nikoschalikias/pcb-n-dap/ord/SKMBT_C28015102014001.pdf

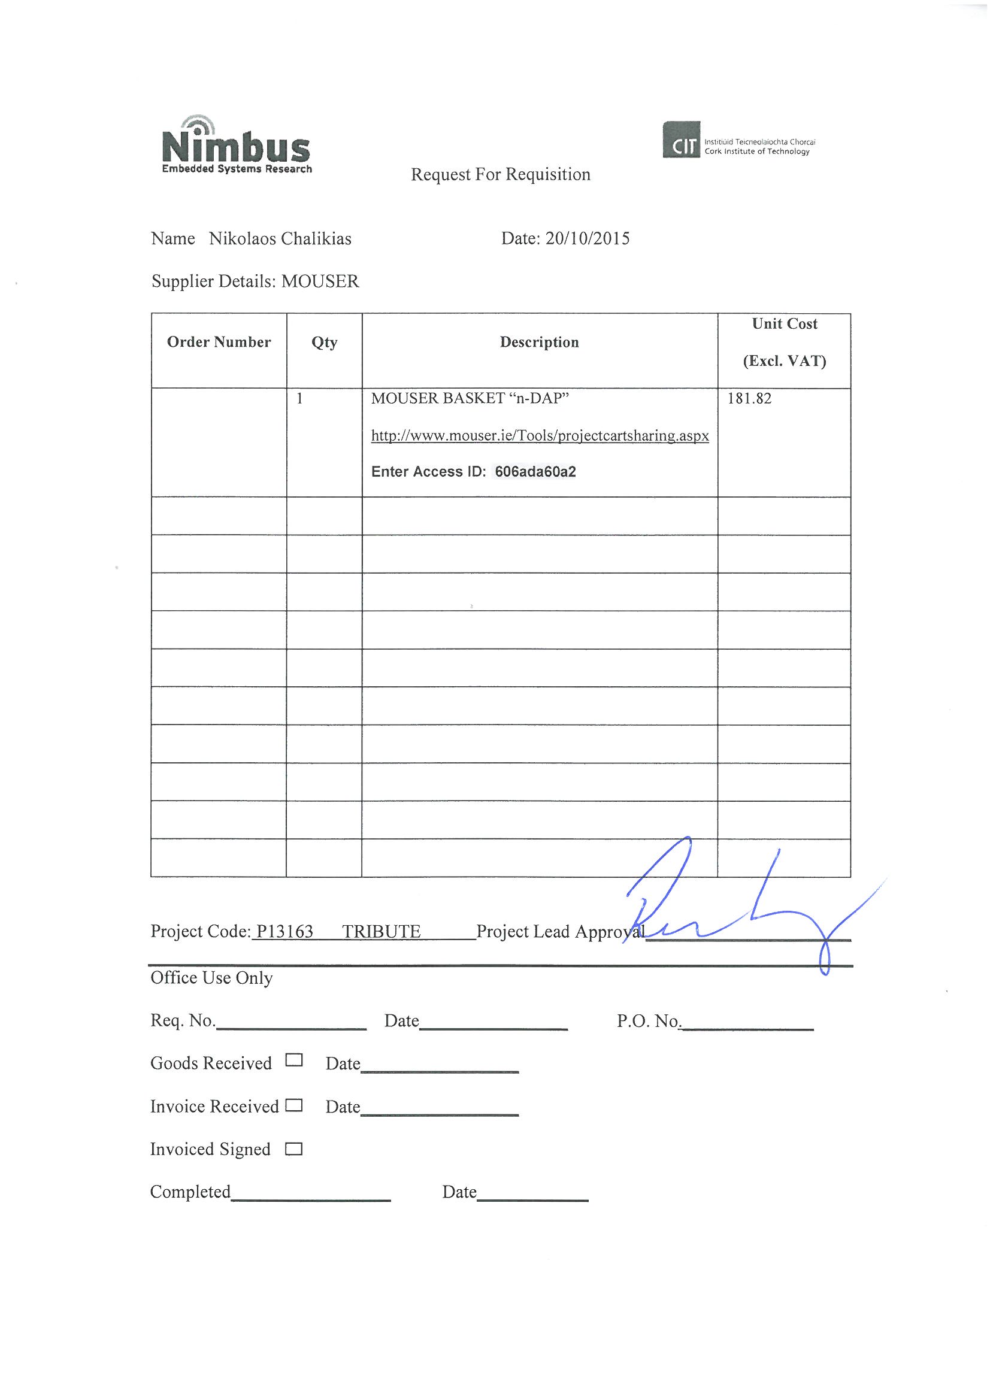
[picture p5: page 1]
