nikoschalikias/pcb-n-dap/ord/SKMBT_C28015101914000.pdf

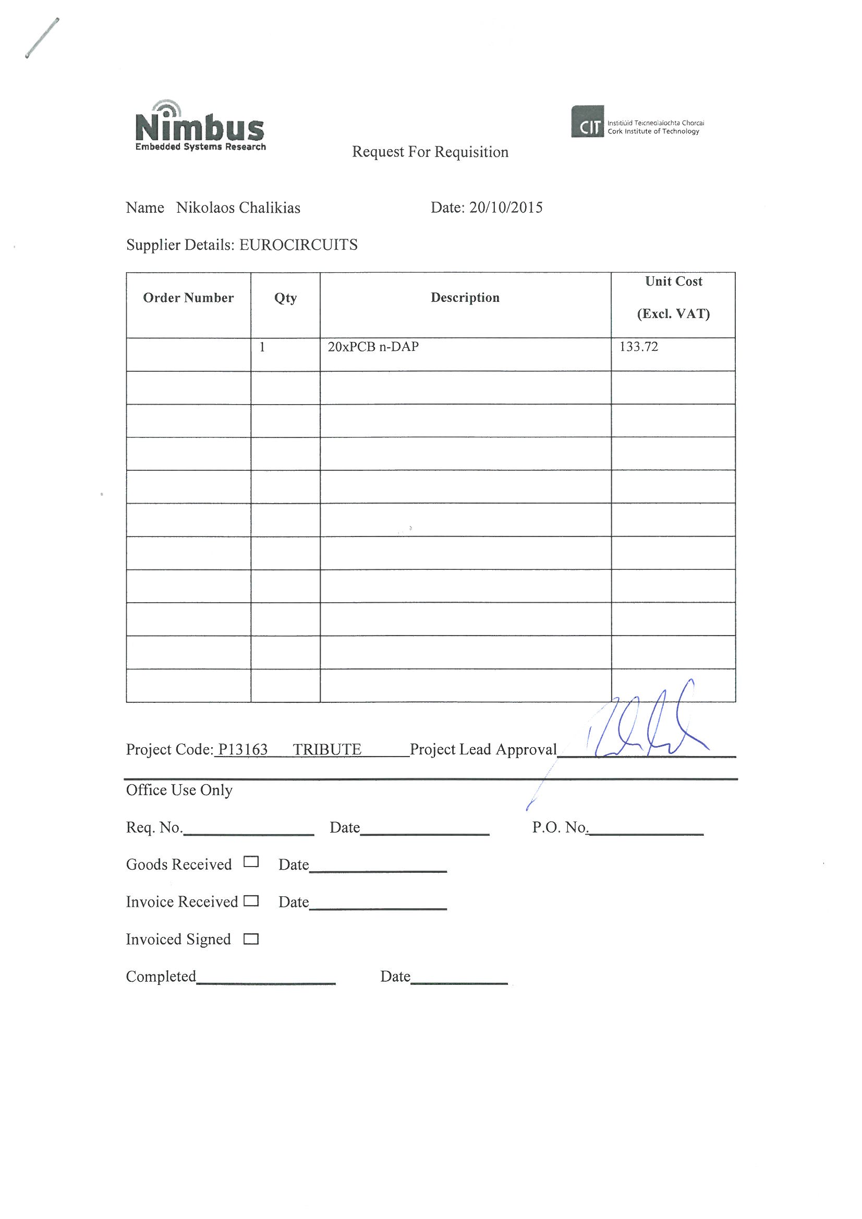
[picture p6: page 1]
