nikoschalikias/pcb-n-dap/template/3D.PDF

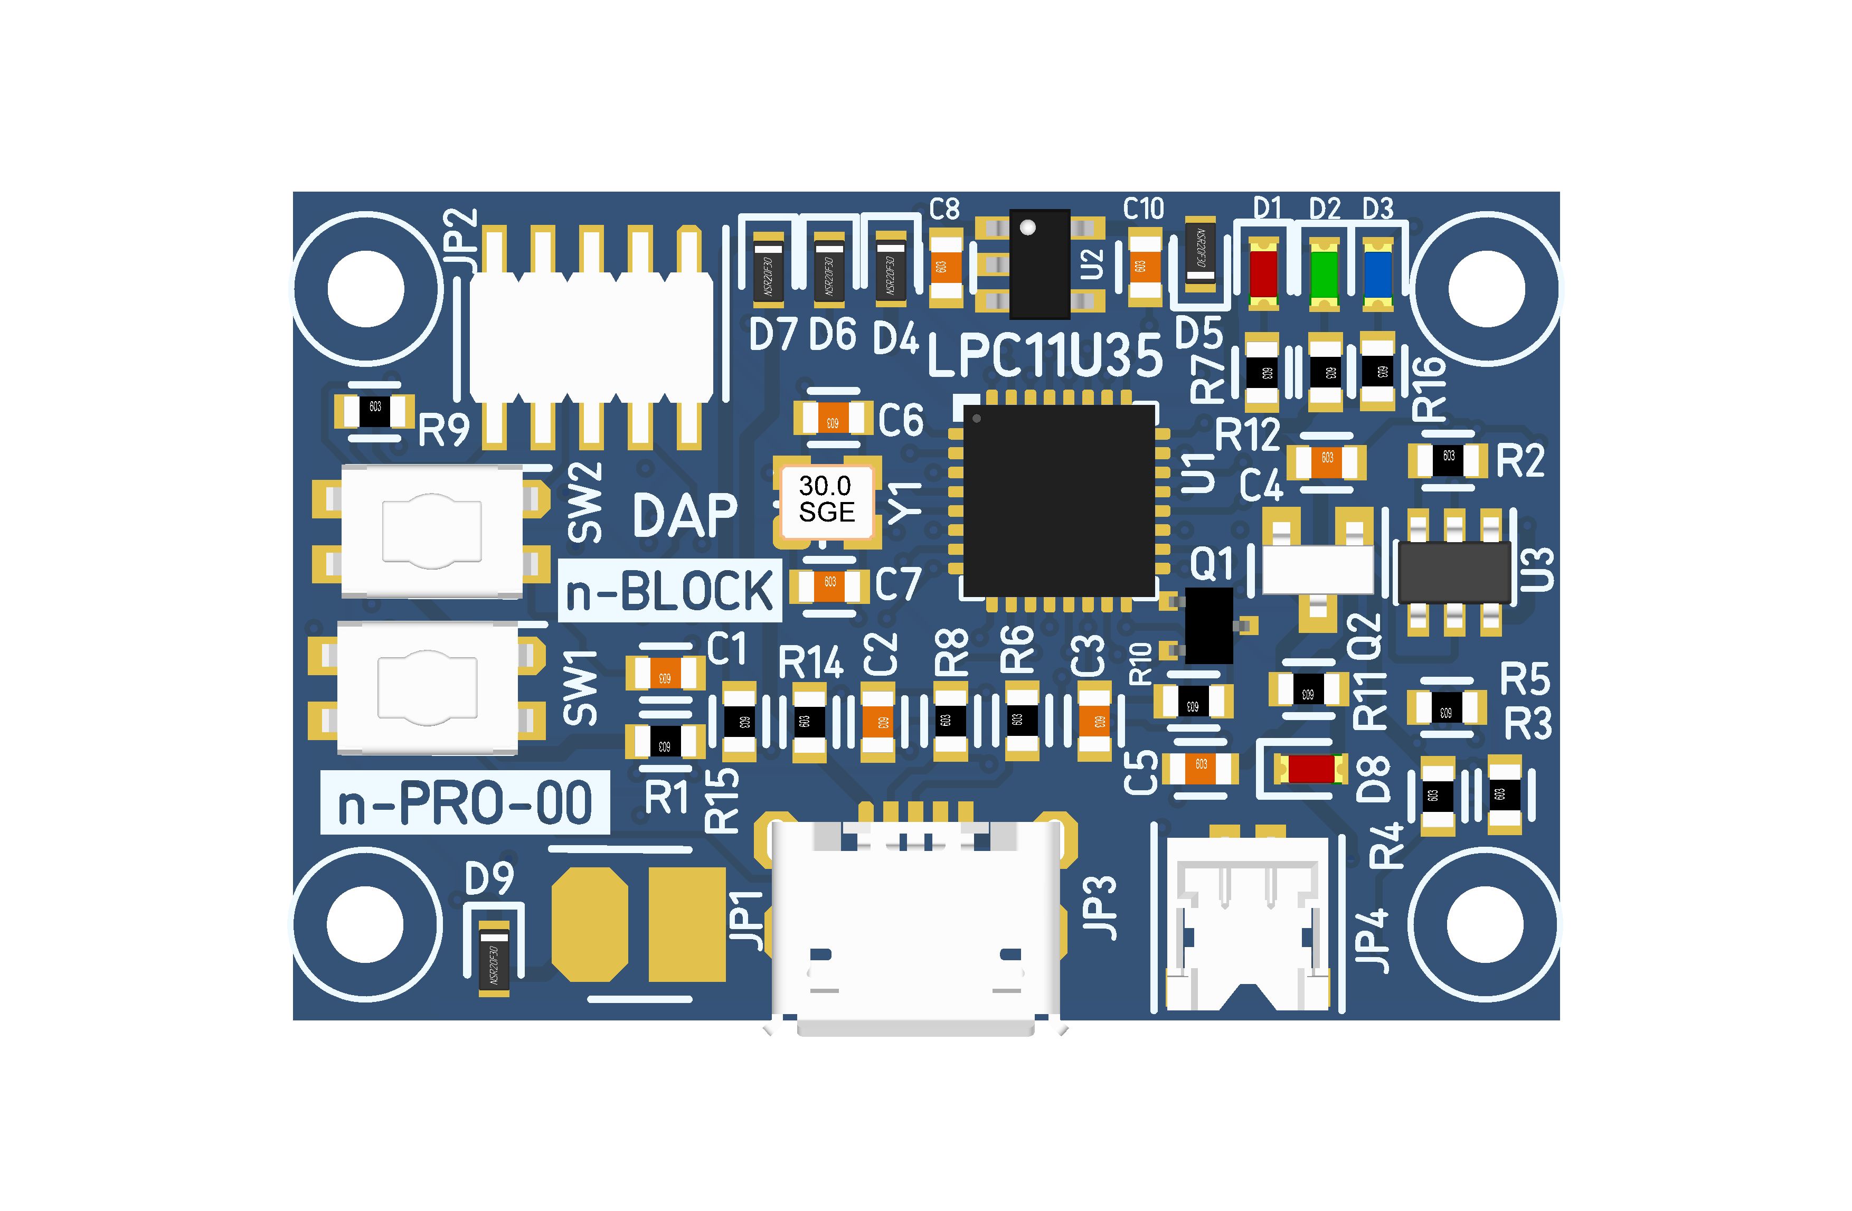
[picture p27: page 3]

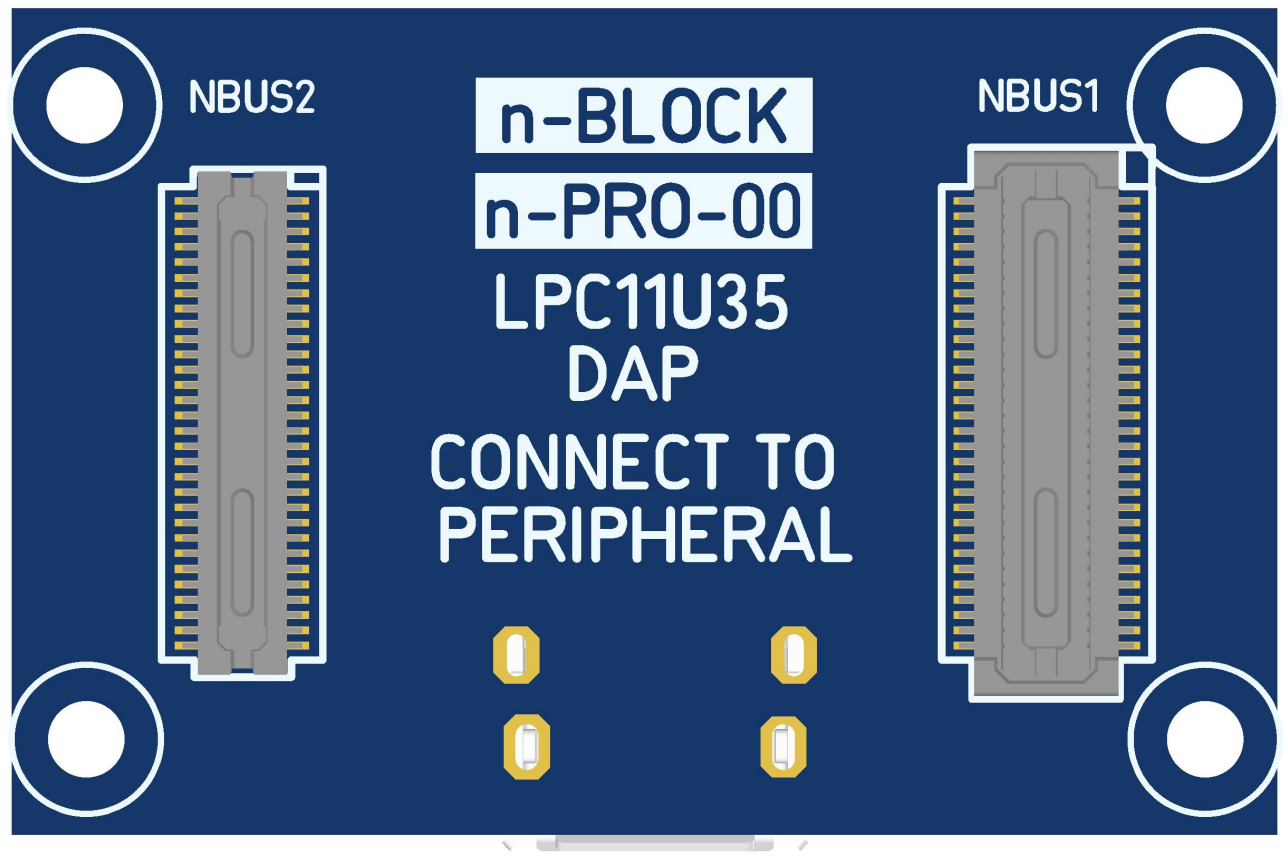
[picture p28: page 4]

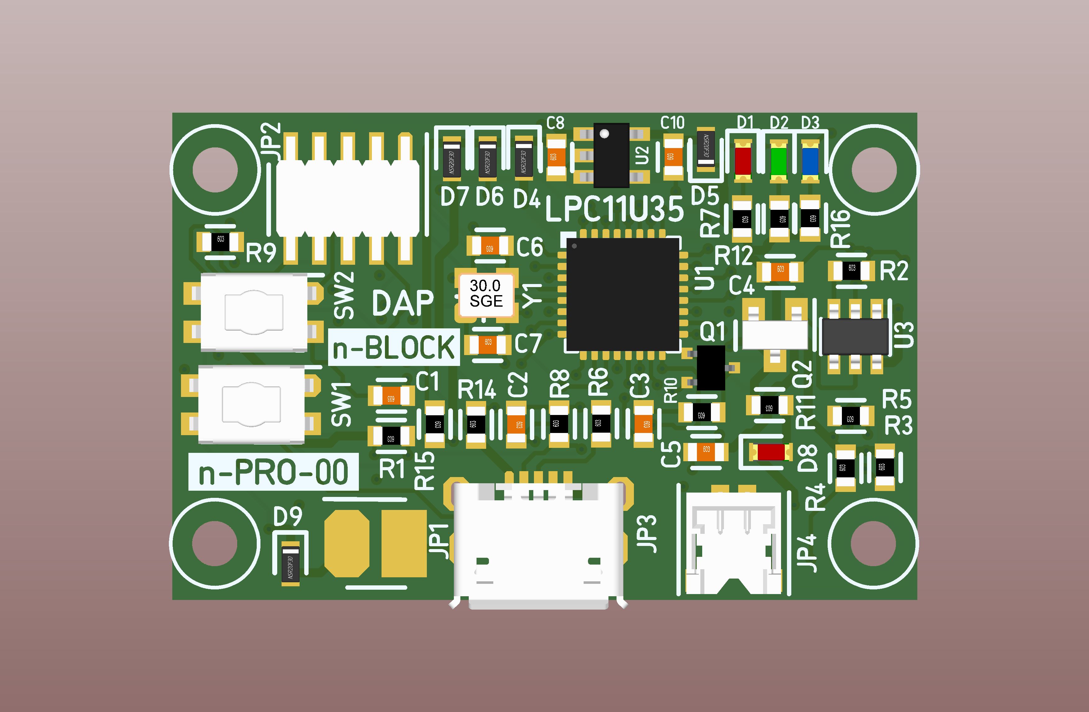
[picture p29: page 5]

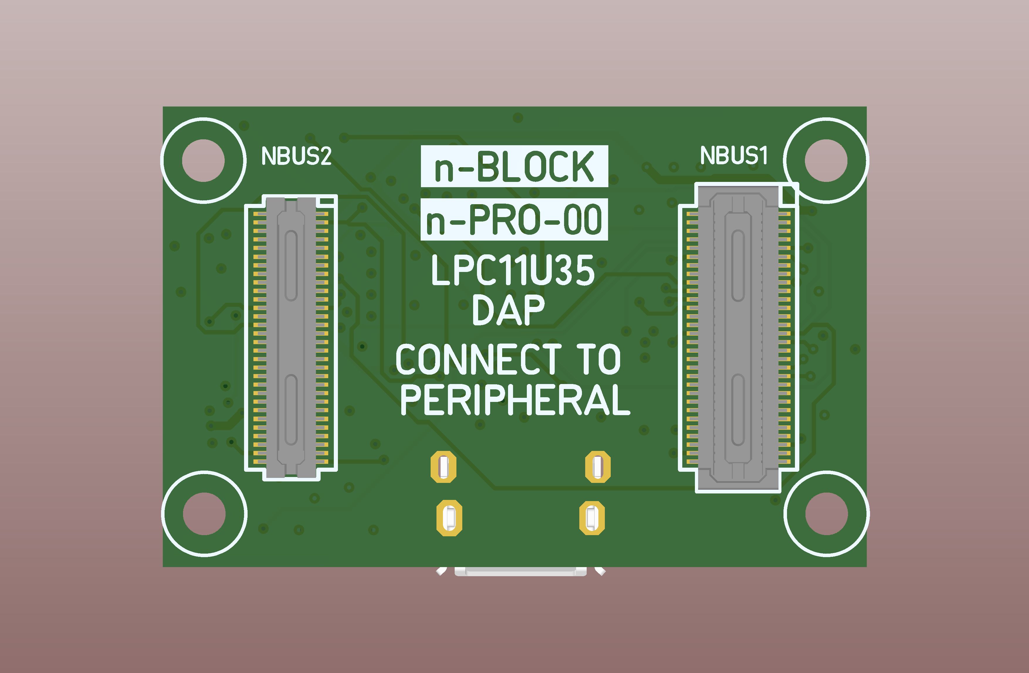
[picture p30: page 6]
