nikoschalikias/pcb-n-dap/asm/placeplan_mech15_smartpdf.PDF

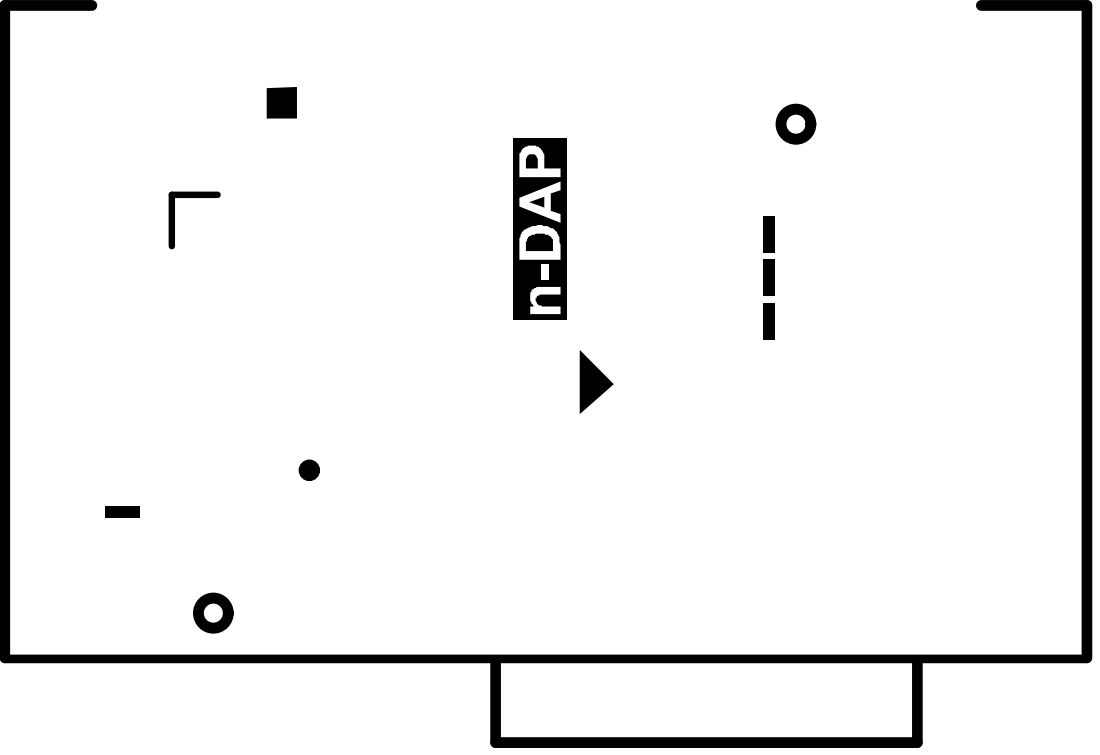
[picture p31: page 1]

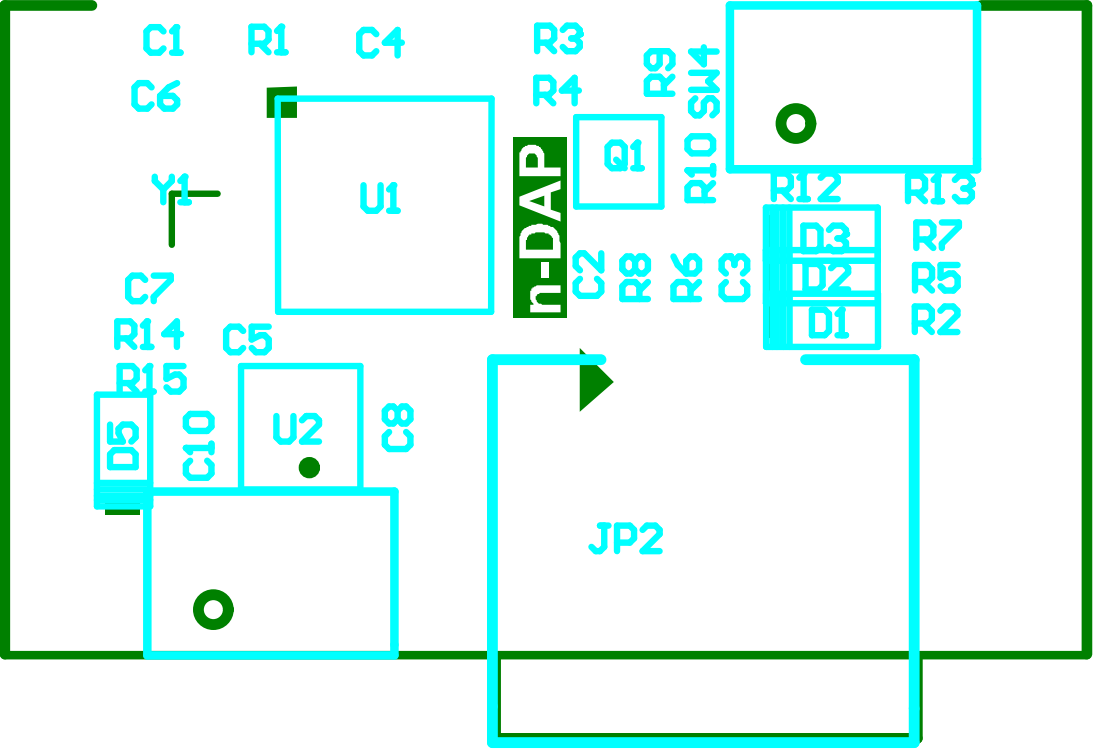
[picture p32: page 2]
